wzwqoo/fmcw_10ghz_radar/rf_frontend/ads/3RX_coupling.png

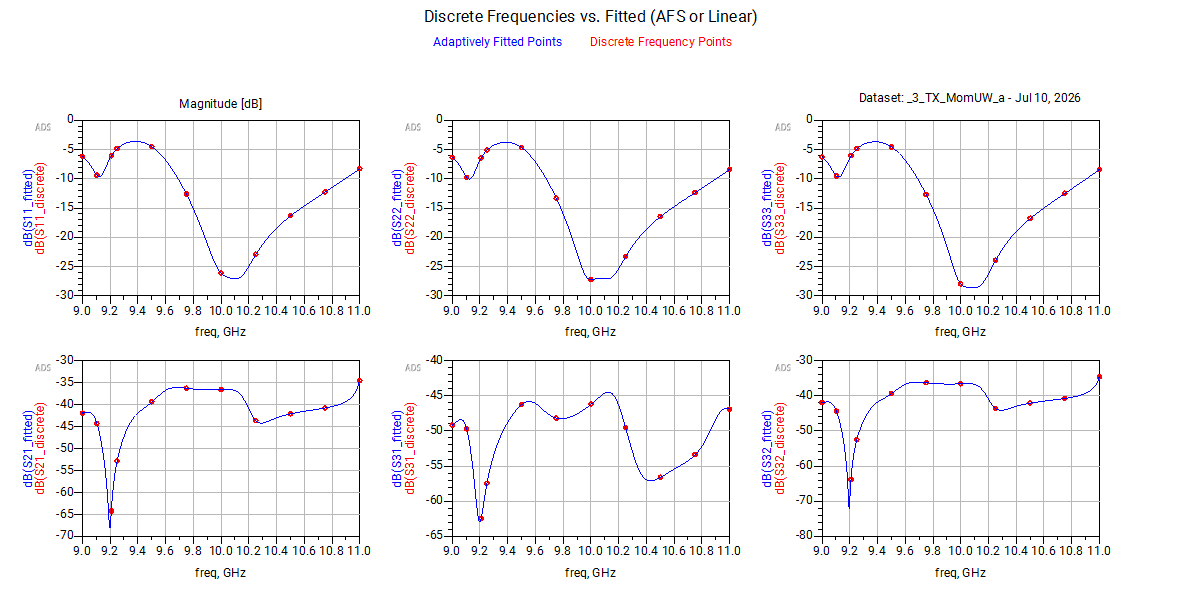
rf_frontend/ads/3RX_coupling.png
