wzwqoo/fmcw_10ghz_radar/rf_frontend/ads/LNA_gain.png

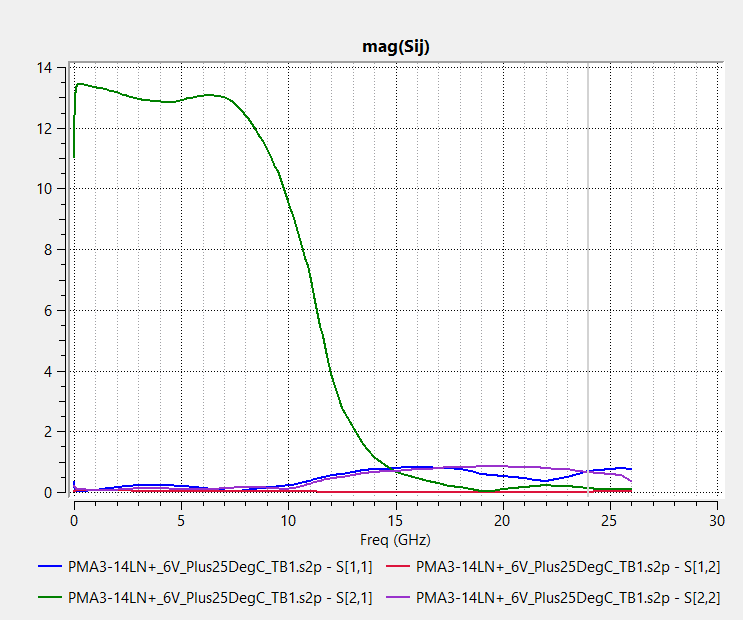
rf_frontend/ads/LNA_gain.png
