wzwqoo/fmcw_10ghz_radar/rf_frontend/ads/LO_tree.png

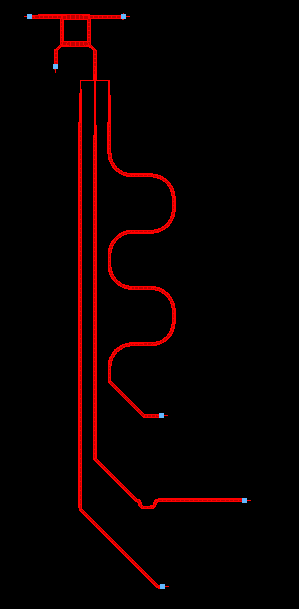
rf_frontend/ads/LO_tree.png
