wzwqoo/fmcw_10ghz_radar/rf_frontend/ads/TX_RX_isolation.png

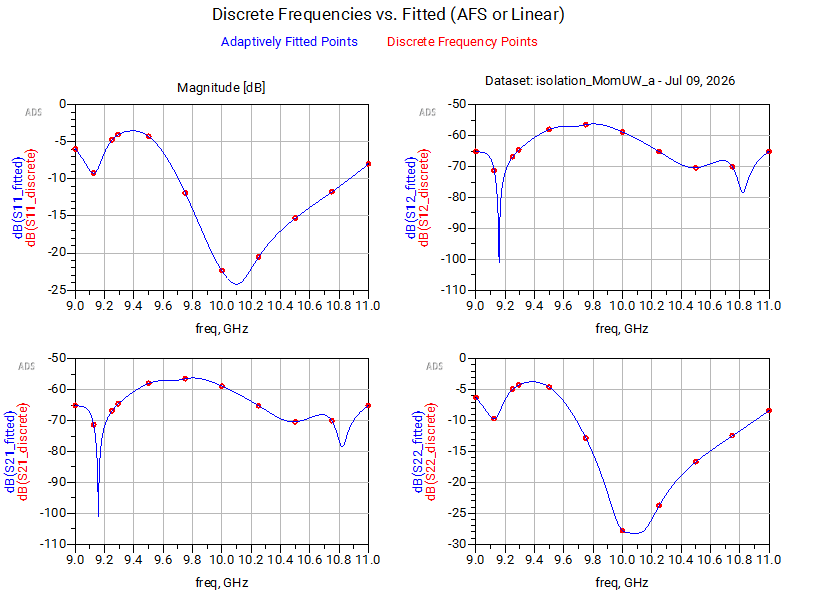
rf_frontend/ads/TX_RX_isolation.png
