wzwqoo/fmcw_10ghz_radar/rf_frontend/ads/coupler_result.png

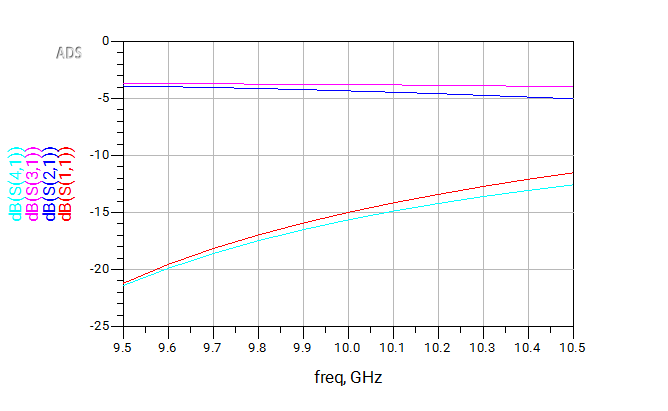
rf_frontend/ads/coupler_result.png
