wzwqoo/fmcw_10ghz_radar/rf_frontend/ads/LO_tree_result.png

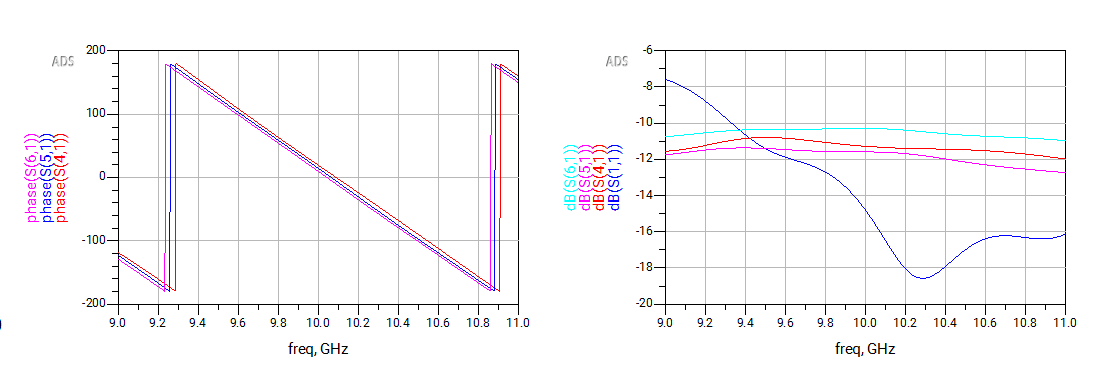
rf_frontend/ads/LO_tree_result.png
