wzwqoo/fmcw_10ghz_radar/rf_frontend/ads/patch_antenna_result.png

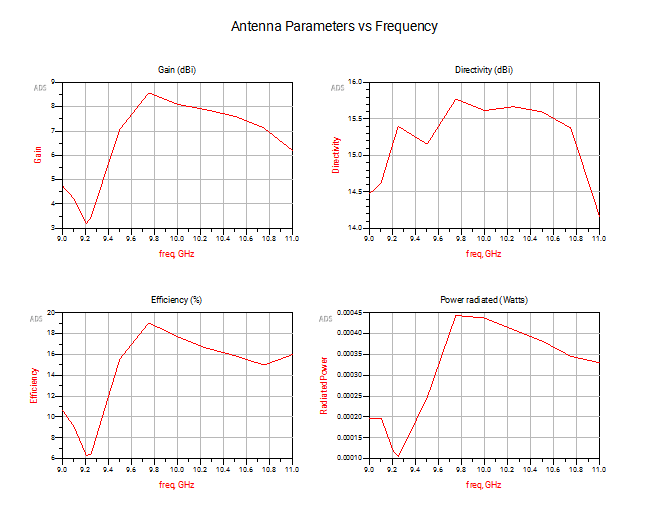
rf_frontend/ads/patch_antenna_result.png
