wzwqoo/fmcw_10ghz_radar/rf_frontend/ads/splitter_result.png

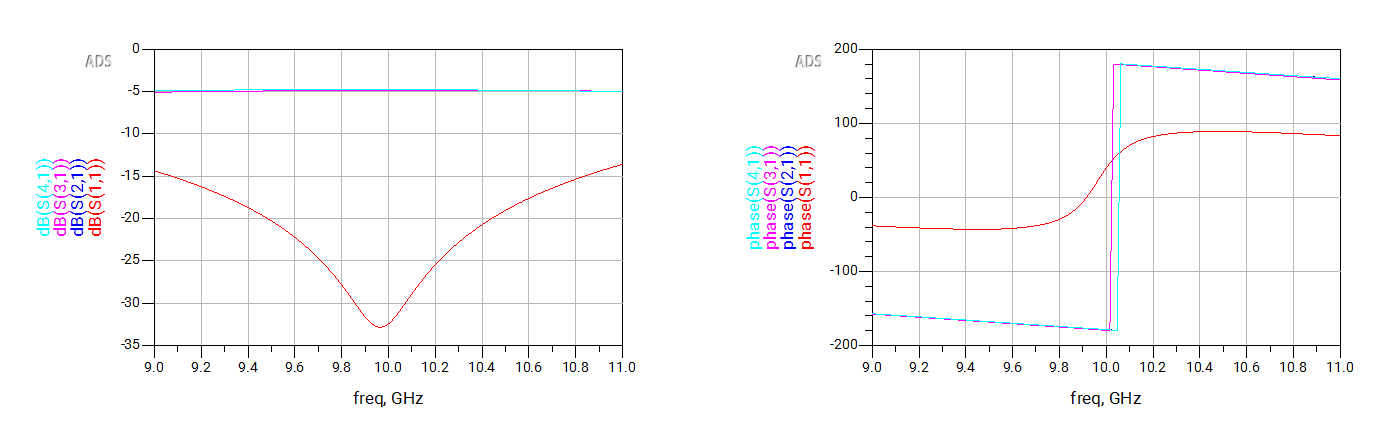
rf_frontend/ads/splitter_result.png
