wzwqoo/fmcw_10ghz_radar/carrier_board/ov9281/ETH.kicad_sch

## KiCad design carrier_board/ov9281/ETH.kicad_sch (2026-09-03)

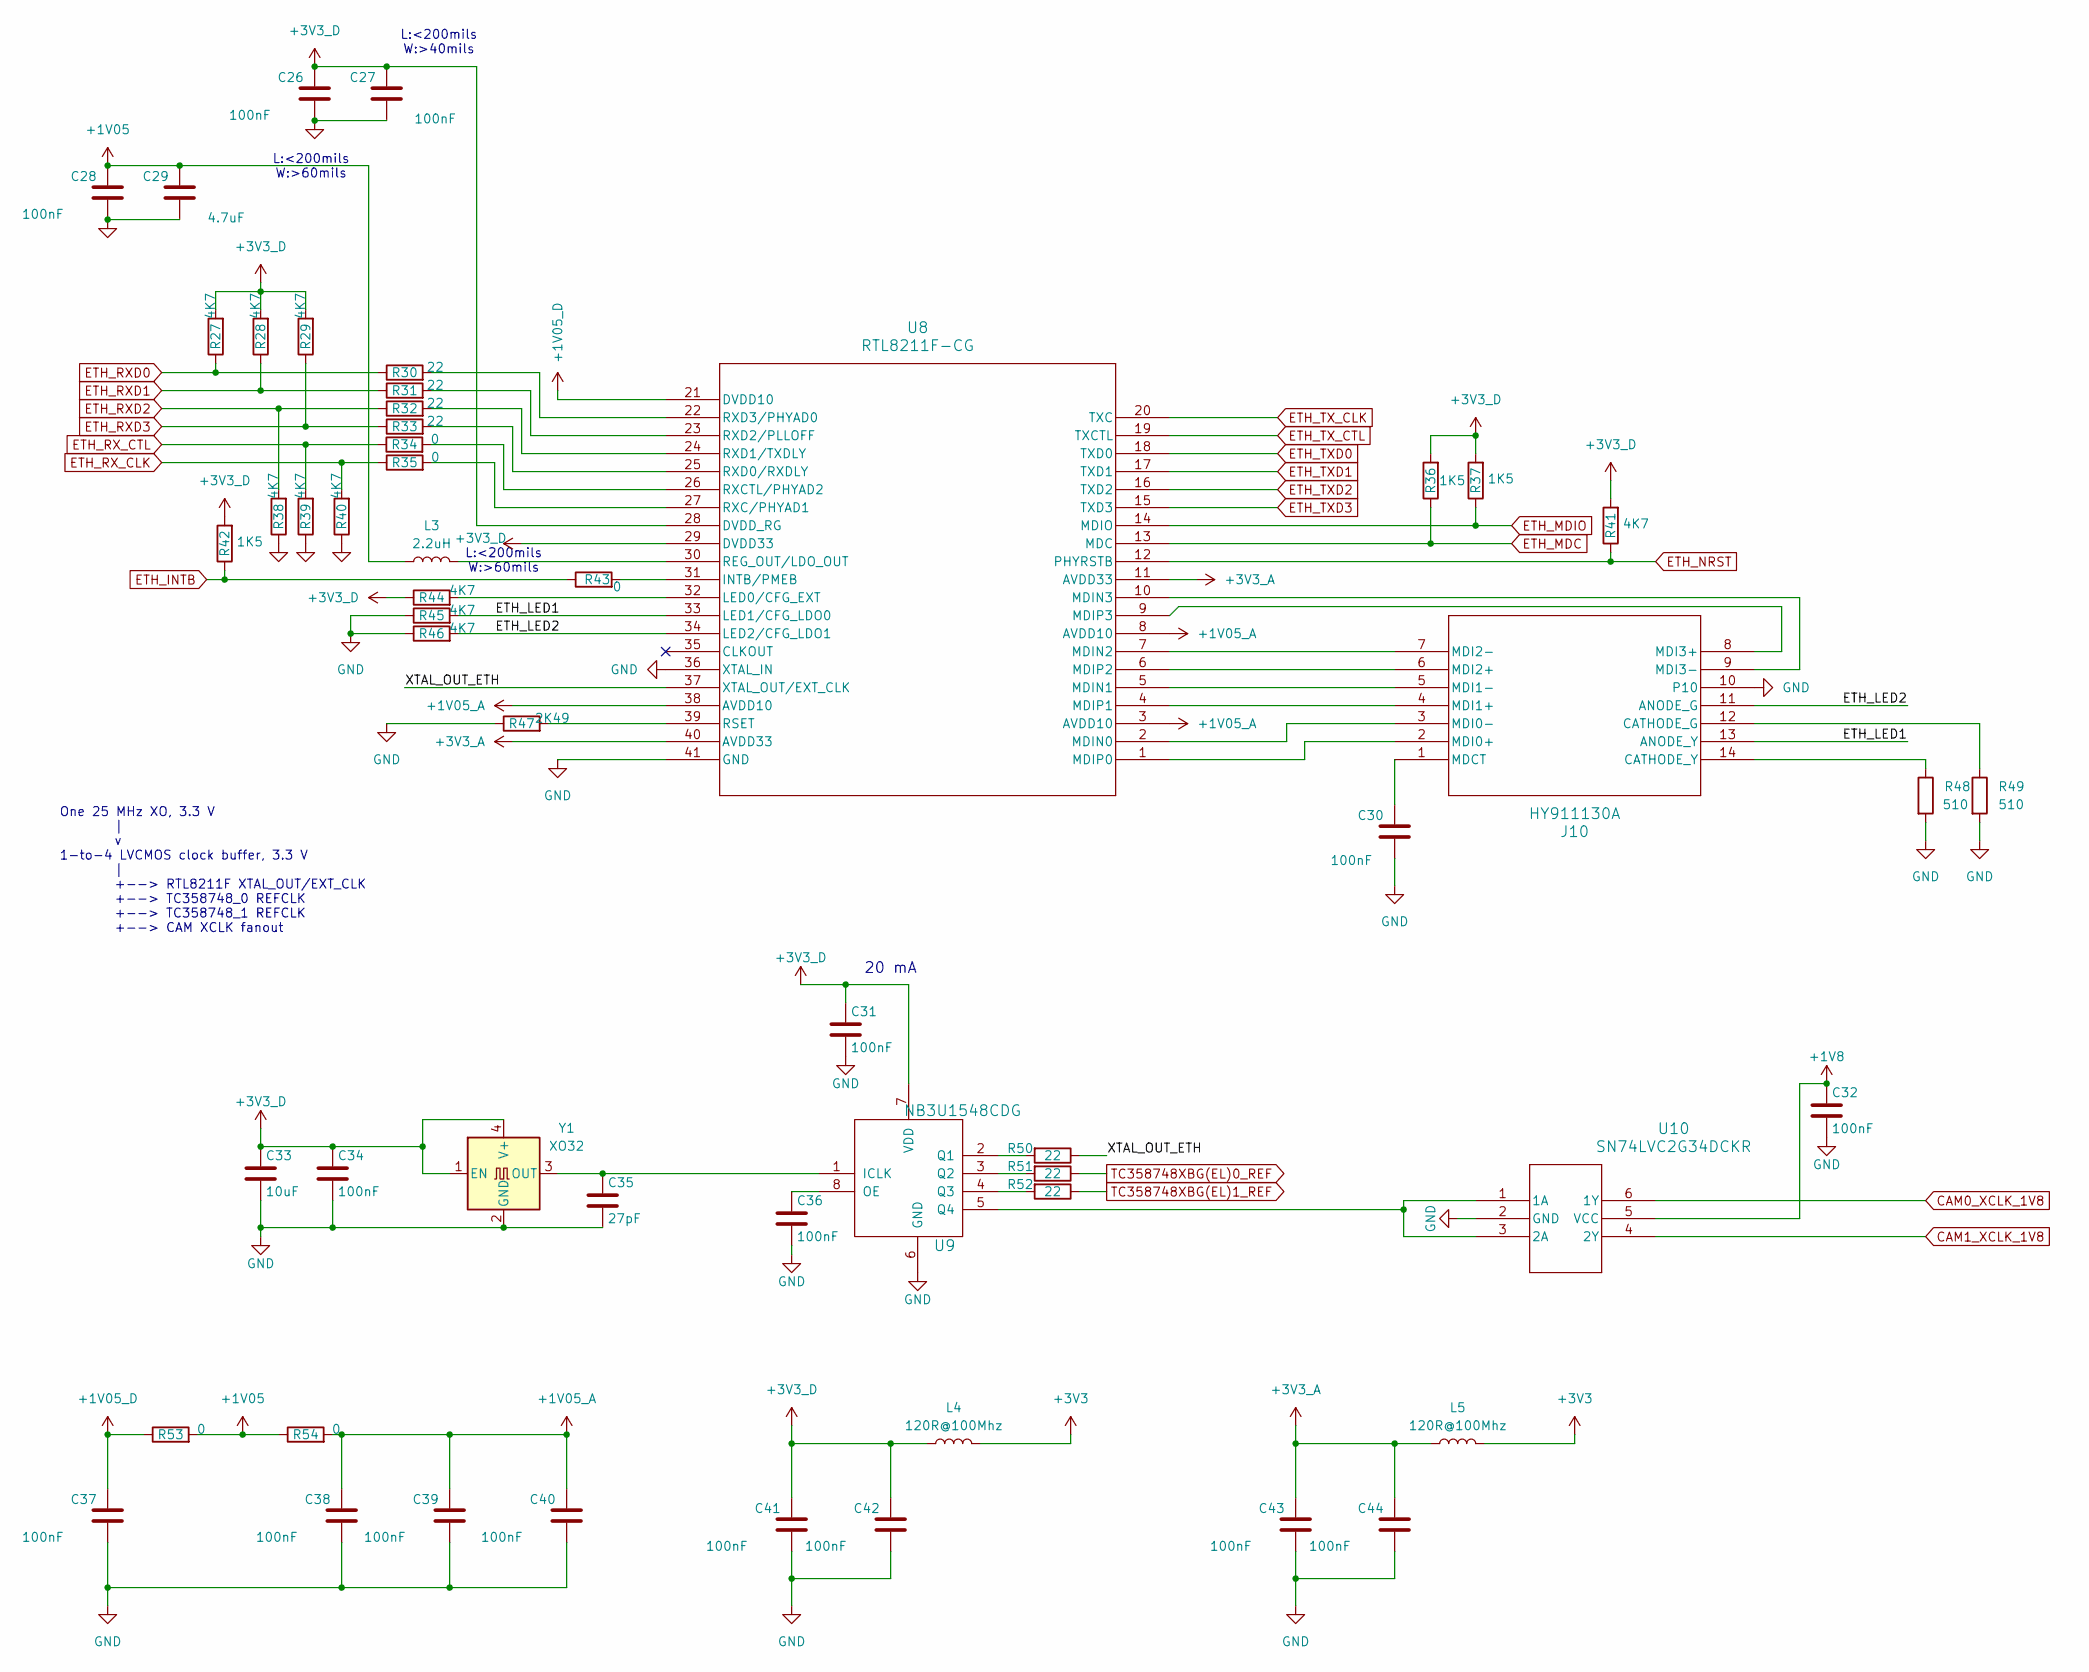
[picture p39: schematic ETH.kicad_sch]

Parts:
C26, C27, C28, C30, C31, C32, C34, C36, C37, C38, C39, C40, C41, C42, C43, C44: 100nF; C_0805_2012Metric; Part# x; LCSC Part # x
C29: 4.7uF; C_0805_2012Metric; Part# CC0805KKX7R8BB475; LCSC Part # C354262
C33: 10uF; C_0805_2012Metric; Part# CC0805KKX5R8BB106; LCSC Part # C89831
C35: 27pF; C_0805_2012Metric; Part# x; LCSC Part # x
J10: HY911130A; HY911130A_HAN; LCSC Part # C55679
L3: 2.2uH; L_0805_2012Metric; Part# MLP2012H2R2MT0S1; LCSC Part # C383369
L4, L5: 120R@100Mhz; L_0805_2012Metric; Part# UPZ2012E121-4R0TF; LCSC Part # C97001
R27, R28, R29, R38, R39, R40, R41, R44, R45, R46: 4K7; R_0805_2012Metric; Part# x; LCSC Part # x
R30, R31, R32, R33, R50, R51, R52: 22; R_0805_2012Metric; Part# RC0805JR-0722RL; LCSC Part # C108406
R34, R35, R43, R53, R54: 0; R_0805_2012Metric; Part# RC0805JR-070RL; LCSC Part # C96345
R36, R37, R42: 1K5; R_0805_2012Metric; Part# RC0805FR-071K5L; LCSC Part # C114555
R47: 2K49; R_0805_2012Metric; Part# AC0805FR-7W2K49L; LCSC Part # C727992
R48, R49: 510; R_0805_2012Metric; Part# RC0805FR-07510RL; LCSC Part # C114563
U8: RTL8211F-CG; RTL8211F-CG_RTK; LCSC Part # C187932
U9: NB3U1548CDG; SOIC-8_5.3x5.3mm_P1.27mm; LCSC Part # C603365
U10: SN74LVC2G34DCKR; SOT-363_SC-70-6; LCSC Part # C14461
Y1: XO32; Oscillator_SMD_EuroQuartz_XO32-4Pin_3.2x2.5mm; Part# OT322525MJBA4SL; LCSC Part # C669088

Connections:
+1V05: C28.1, C29.1, L3.1, R53.2, R54.1
+1V05_A: C38.1, C39.1, C40.1, R54.2, U8.3 (AVDD10), U8.8 (AVDD10), U8.38 (AVDD10)
+1V05_D: C37.1, R53.1, U8.21 (DVDD10)
+1V8: C32.1, U10.5 (VCC)
+3V3: L4.2, L5.2
+3V3_A: C43.1, C44.1, L5.1, U8.11 (AVDD33), U8.40 (AVDD33)
+3V3_D: C26.1, C27.1, C31.1, C33.1, C34.1, C41.1, C42.1, L4.1, R27.2, R28.2, R29.2, R36.2, R37.2, R41.2, R42.2, R44.1, U8.28 (DVDD_RG), U8.29 (DVDD33), U9.7 (VDD), Y1.1 (EN), Y1.4 (V+)
CAM0_XCLK_1V8: U10.6 (1Y)
CAM1_XCLK_1V8: U10.4 (2Y)
ETH_INTB: R42.1, R43.1
ETH_LED1: J10.13 (ANODE_Y), R45.2, U8.33 (LED1/CFG_LDO0)
ETH_LED2: J10.11 (ANODE_G), R46.2, U8.34 (LED2/CFG_LDO1)
ETH_MDC: R36.1, U8.13 (MDC)
ETH_MDIO: R37.1, U8.14 (MDIO)
ETH_NRST: R41.1, U8.12 (PHYRSTB)
ETH_RXD0: R27.1, R30.1
ETH_RXD1: R28.1, R31.1
ETH_RXD2: R32.1, R38.2
ETH_RXD3: R29.1, R33.1
ETH_RX_CLK: R35.1, R40.2
ETH_RX_CTL: R34.1, R39.2
ETH_TXD0: U8.18 (TXD0)
ETH_TXD1: U8.17 (TXD1)
ETH_TXD2: U8.16 (TXD2)
ETH_TXD3: U8.15 (TXD3)
ETH_TX_CLK: U8.20 (TXC)
ETH_TX_CTL: U8.19 (TXCTL)
GND: C26.2, C27.2, C28.2, C29.2, C30.2, C31.2, C32.2, C33.2, C34.2, C35.2, C36.2, C37.2, C38.2, C39.2, C40.2, C41.2, C42.2, C43.2, C44.2, J10.10, R38.1, R39.1, R40.1, R45.1, R46.1, R47.1, R48.2, R49.2, U8.36 (XTAL_IN), U8.41 (GND), U9.6 (GND), U10.2 (GND), Y1.2 (GND)
unnamed: C30.1, J10.1 (MDCT)
unnamed: C35.1, U9.1 (ICLK), Y1.3 (OUT)
unnamed: C36.1, U9.8 (OE)
unnamed: J10.2 (MDI0+), U8.1 (MDIP0)
unnamed: J10.3 (MDI0-), U8.2 (MDIN0)
unnamed: J10.4 (MDI1+), U8.4 (MDIP1)
unnamed: J10.5 (MDI1-), U8.5 (MDIN1)
unnamed: J10.6 (MDI2+), U8.6 (MDIP2)
unnamed: J10.7 (MDI2-), U8.7 (MDIN2)
unnamed: J10.8 (MDI3+), U8.9 (MDIP3)
unnamed: J10.9 (MDI3-), U8.10 (MDIN3)
unnamed: J10.12 (CATHODE_G), R49.1
unnamed: J10.14 (CATHODE_Y), R48.1
unnamed: L3.2, U8.30 (REG_OUT/LDO_OUT)
unnamed: R30.2, U8.22 (RXD3/PHYAD0)
unnamed: R31.2, U8.23 (RXD2/PLLOFF)
unnamed: R32.2, U8.24 (RXD1/TXDLY)
unnamed: R33.2, U8.25 (RXD0/RXDLY)
unnamed: R34.2, U8.26 (RXCTL/PHYAD2)
unnamed: R35.2, U8.27 (RXC/PHYAD1)
unnamed: R43.2, U8.31 (INTB/PMEB)
unnamed: R44.2, U8.32 (LED0/CFG_EXT)
unnamed: R47.2, U8.39 (RSET)
unnamed: R50.2, U9.2 (Q1)
unnamed: R51.2, U9.3 (Q2)
unnamed: R52.2, U9.4 (Q3)
unnamed: U9.5 (Q4), U10.1 (1A), U10.3 (2A)
TC358748XBG(EL)0_REF: R51.1
TC358748XBG(EL)1_REF: R52.1
XTAL_OUT_ETH: R50.1, U8.37 (XTAL_OUT/EXT_CLK)

Notes on the sheet:
L:<200mils W:>40mils
L:<200mils W:>60mils
One 25 MHz XO, 3.3 V | v 1-to-4 LVCMOS clock buffer, 3.3 V | +--> RTL8211F XTAL_OUT/EXT_CLK +--> TC358748_0 REFCLK +--> TC358748_1 REFCLK +--> CAM XCLK fanout
20 mA
