wzwqoo/fmcw_10ghz_radar/carrier_board/ov9281/FMCW.kicad_sch

## KiCad design carrier_board/ov9281/FMCW.kicad_sch (2026-09-03)

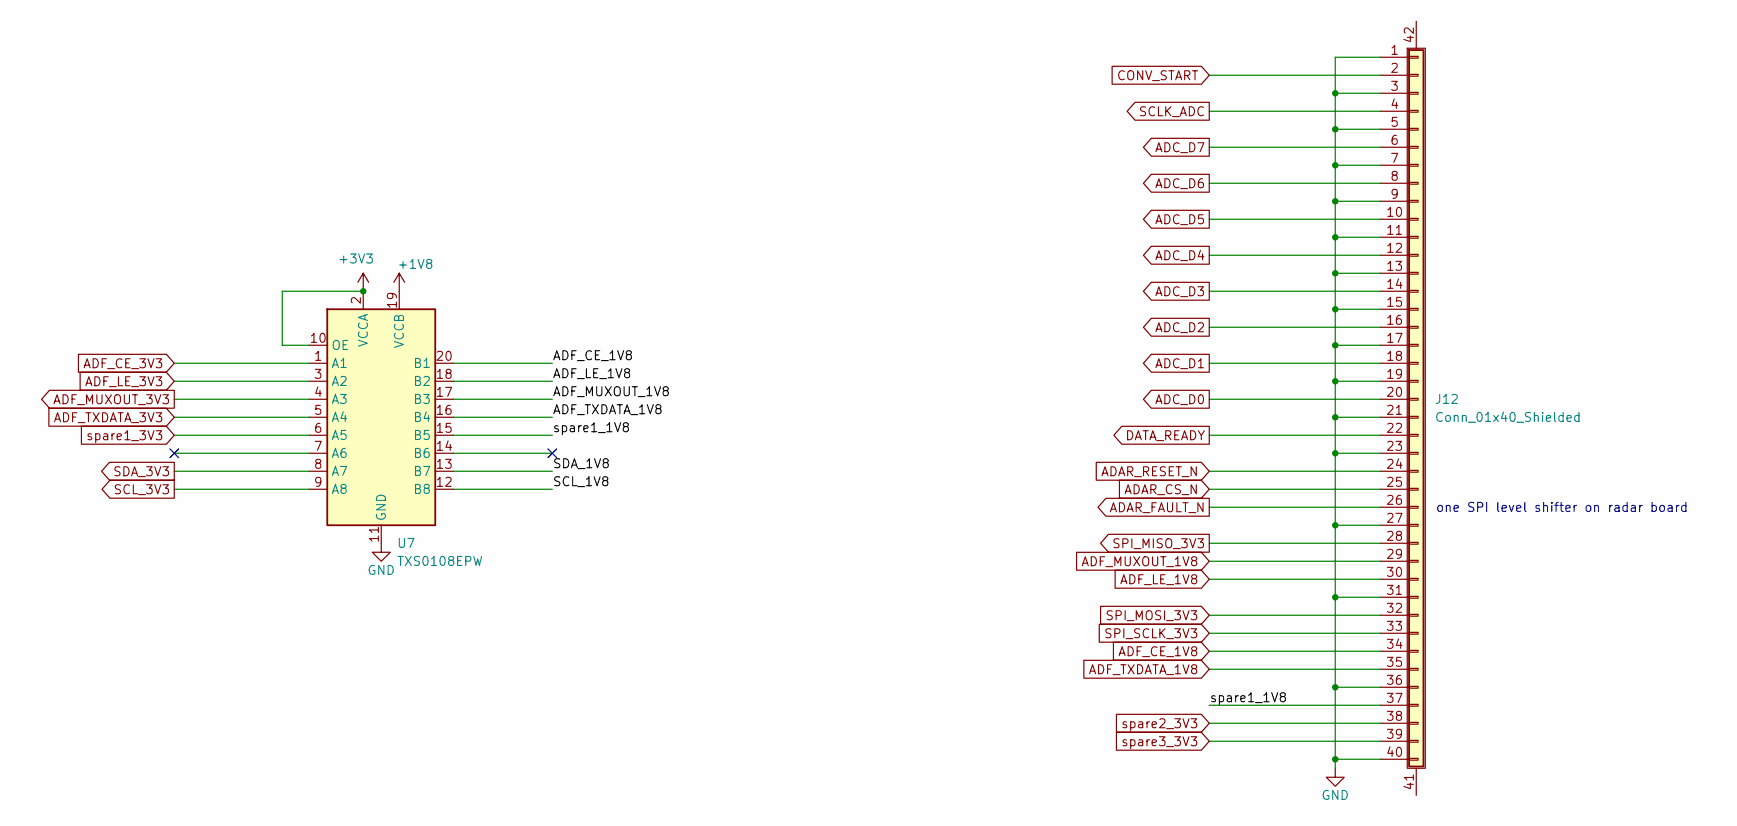
[picture p40: schematic FMCW.kicad_sch]

Parts:
J12: Conn_01x40_Shielded; FPC-SMD_40P-P0.50_XUNPU_FPC-05FB-40PH20; Part# FPC-05FB-40PH20; LCSC Part # C2856837
U7: TXS0108EPW; TSSOP-20_4.4x6.5mm_P0.65mm; LCSC Part # C17206

Connections:
+1V8: U7.19 (VCCB)
+3V3: U7.2 (VCCA), U7.10 (OE)
ADAR_CS_N: J12.25
ADAR_FAULT_N: J12.26
ADAR_RESET_N: J12.24
ADC_D0: J12.20
ADC_D1: J12.18
ADC_D2: J12.16
ADC_D3: J12.14
ADC_D4: J12.12
ADC_D5: J12.10
ADC_D6: J12.8
ADC_D7: J12.6
ADF_CE_1V8: J12.34, U7.20 (B1)
ADF_CE_3V3: U7.1 (A1)
ADF_LE_1V8: J12.30, U7.18 (B2)
ADF_LE_3V3: U7.3 (A2)
ADF_MUXOUT_1V8: J12.29, U7.17 (B3)
ADF_MUXOUT_3V3: U7.4 (A3)
ADF_TXDATA_1V8: J12.35, U7.16 (B4)
ADF_TXDATA_3V3: U7.5 (A4)
CONV_START: J12.2
DATA_READY: J12.22
GND: J12.1, J12.3, J12.5, J12.7, J12.9, J12.11, J12.13, J12.15, J12.17, J12.19, J12.21, J12.23, J12.27, J12.31, J12.36, J12.40, U7.11 (GND)
SCLK_ADC: J12.4
SCL_1V8: U7.12 (B8)
SCL_3V3: U7.9 (A8)
SDA_1V8: U7.13 (B7)
SDA_3V3: U7.8 (A7)
SPI_MISO_3V3: J12.28
SPI_MOSI_3V3: J12.32
SPI_SCLK_3V3: J12.33
spare1_1V8: J12.37, U7.15 (B5)
spare1_3V3: U7.6 (A5)
spare2_3V3: J12.38
spare3_3V3: J12.39

Notes on the sheet:
one SPI level shifter on radar board
