wzwqoo/fmcw_10ghz_radar/carrier_board/ov9281/FPGA.kicad_sch

## KiCad design carrier_board/ov9281/FPGA.kicad_sch (2026-09-03)

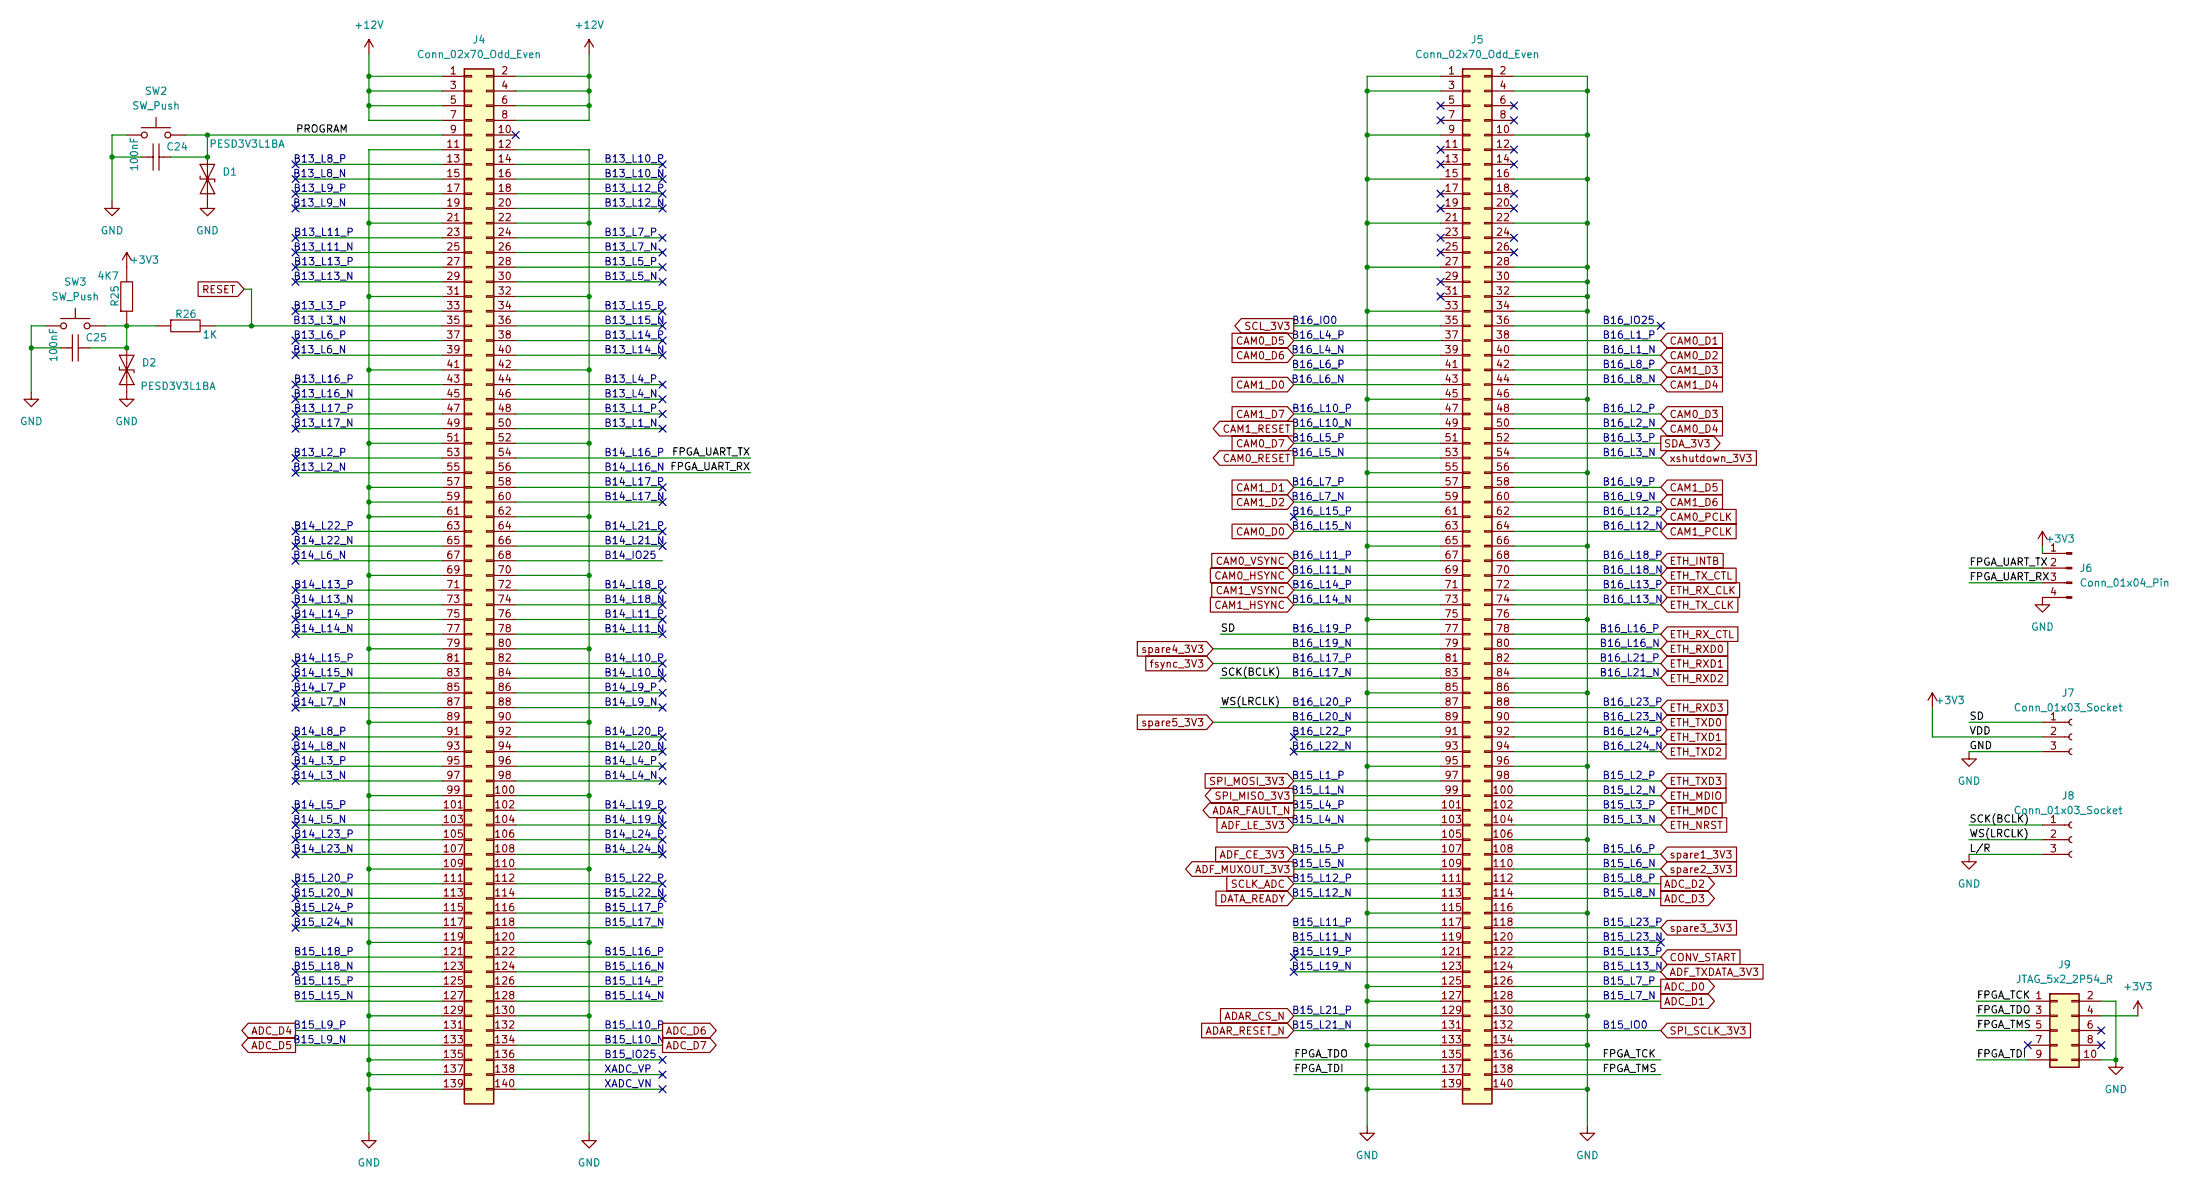
[picture p41: schematic FPGA.kicad_sch]

Parts:
C24, C25: 100nF; C_0805_2012Metric; TOLERANCE ±10%; RATINGS 16V; X7R; MANUFACTURER PART NUMBE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 CC0402KRX7R7BB103; LCSC Part # x
D1, D2: PESD3V3L1BA; D_SOD-323; Part# PESD3V3L1BA; LCSC Part # C54334012
J4, J5: Conn_02x70_Odd_Even; CONN-SMD_140P-P0.50_B2BM-2X70-0P5_BZOOC; Part# x; LCSC Part # x
J6: Conn_01x04_Pin; PinHeader_1x04_P2.54mm_Vertical; Part# x; LCSC Part # x
J7, J8: Conn_01x03_Socket; PinSocket_1x03_P2.54mm_Vertical; Part# x; LCSC Part # x
J9: JTAG_5x2_2P54_R; PinHeader_2x05_P2.54mm_Horizontal; Part# TSW-105-08-F-D-RA; LCSC Part # C6292590
R25: 4K7; R_0805_2012Metric; RATINGS 1/16 W; TOLERANCE ±5%; MANUFACTURER PART NUMBE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 RC0402JR-073K3L; LCSC Part # x
R26: 1K; R_0805_2012Metric; RATINGS 1/16 W; TOLERANCE ±5%; MANUFACTURER PART NUMBE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 RC0402JR-073K3L; LCSC Part # C100046
SW2, SW3: SW_Push; SW_Push_SPST_NO_Alps_SKRK; Part# SKRKAHE020; LCSC Part # C202388

Connections:
+3V3: J6.1, J7.2, J9.4, R25.2
+12V: J4.1, J4.2, J4.3, J4.4, J4.5, J4.6, J4.7, J4.8
ADAR_CS_N: J5.129
ADAR_FAULT_N: J5.101
ADAR_RESET_N: J5.131
ADC_D0: J5.126
ADC_D1: J5.128
ADC_D2: J5.112
ADC_D3: J5.114
ADC_D4: J4.131
ADC_D5: J4.133
ADC_D6: J4.132
ADC_D7: J4.134
ADF_CE_3V3: J5.107
ADF_LE_3V3: J5.103
ADF_MUXOUT_3V3: J5.109
ADF_TXDATA_3V3: J5.124
CAM0_D0: J5.63
CAM0_D1: J5.38
CAM0_D2: J5.40
CAM0_D3: J5.48
CAM0_D4: J5.50
CAM0_D5: J5.37
CAM0_D6: J5.39
CAM0_D7: J5.51
CAM0_HSYNC: J5.69
CAM0_PCLK: J5.62
CAM0_RESET: J5.53
CAM0_VSYNC: J5.67
CAM1_D0: J5.43
CAM1_D1: J5.57
CAM1_D2: J5.59
CAM1_D3: J5.42
CAM1_D4: J5.44
CAM1_D5: J5.58
CAM1_D6: J5.60
CAM1_D7: J5.47
CAM1_HSYNC: J5.73
CAM1_PCLK: J5.64
CAM1_RESET: J5.49
CAM1_VSYNC: J5.71
CONV_START: J5.122
DATA_READY: J5.113
ETH_INTB: J5.68
ETH_MDC: J5.102
ETH_MDIO: J5.100
ETH_NRST: J5.104
ETH_RXD0: J5.80
ETH_RXD1: J5.82
ETH_RXD2: J5.84
ETH_RXD3: J5.88
ETH_RX_CLK: J5.72
ETH_RX_CTL: J5.78
ETH_TXD0: J5.90
ETH_TXD1: J5.92
ETH_TXD2: J5.94
ETH_TXD3: J5.98
ETH_TX_CLK: J5.74
ETH_TX_CTL: J5.70
FPGA_TCK: J5.136, J9.1
FPGA_TDI: J5.137, J9.9
FPGA_TDO: J5.135, J9.3
FPGA_TMS: J5.138, J9.5
FPGA_UART_RX: J4.56, J6.3
FPGA_UART_TX: J4.54, J6.2
GND: C24.2, C25.2, D1.1 (A1), D2.1 (A1), J4.11, J4.12, J4.21, J4.22, J4.31, J4.32, J4.41, J4.42, J4.51, J4.52, J4.57, J4.59, J4.61, J4.62, J4.69, J4.70, J4.79, J4.80, J4.89, J4.90, J4.99, J4.100, J4.109, J4.110, J4.119, J4.120, J4.129, J4.130, J4.135, J4.137, J4.139, J5.1, J5.2, J5.3, J5.4, J5.9, J5.10, J5.15, J5.16, J5.21, J5.22, J5.27, J5.28, J5.30, J5.32, J5.33, J5.34, J5.45, J5.46, J5.55, J5.56, J5.65, J5.66, J5.75, J5.76, J5.85, J5.86, J5.95, J5.96, J5.105, J5.106, J5.115, J5.116, J5.125, J5.127, J5.130, J5.133, J5.134, J5.139, J5.140, J6.4, J7.3, J8.3, J9.2, J9.10, SW2.1, SW3.1
unnamed: C25.1, D2.2 (A2), R25.1, R26.1, SW3.2
PROGRAM: C24.1, D1.2 (A2), J4.9, SW2.2
RESET: J4.35, R26.2
SCK(BCLK): J5.83, J8.1
SCLK_ADC: J5.111
SCL_3V3: J5.35
SD: J5.77, J7.1
SDA_3V3: J5.52
SPI_MISO_3V3: J5.99
SPI_MOSI_3V3: J5.97
SPI_SCLK_3V3: J5.132
WS(LRCLK): J5.87, J8.2
fsync_3V3: J5.81
spare1_3V3: J5.108
spare2_3V3: J5.110
spare3_3V3: J5.118
spare4_3V3: J5.79
spare5_3V3: J5.89
xshutdown_3V3: J5.54

Notes on the sheet:
B16_L14_N
B14_L24_P
B14_L15_P
B16_L1_P
B14_L22_N
B15_L5_P
B16_L3_P
B16_L13_N
B15_L17_N
B13_L6_P
B16_L21_N
B14_L14_P
B15_L1_N
B13_L2_P
B15_L24_P
B15_L15_P
B14_IO25
B16_L20_P
B14_L18_P
B13_L13_N
B16_L24_N
B15_L7_P
B13_L16_N
B13_L13_P
B15_L11_N
B15_L21_N
B15_L22_P
B15_L20_P
B13_L1_P
B14_L9_P
B13_L4_P
B13_L14_N
B15_L14_P
B15_L24_N
B16_L11_P
B14_L3_P
B15_L8_N
B13_L8_N
B13_L14_P
B15_L23_P
B16_L24_P
B14_L22_P
B13_L11_P
B16_L3_N
B16_L18_N
B16_L19_N
B16_L21_P
B15_IO25
B15_L1_P
B16_L7_P
B13_L17_N
B16_L10_P
B16_L9_P
B16_L15_N
B13_L11_N
B16_L22_N
B16_L12_N
B15_L12_P
B16_L9_N
B16_L2_N
B15_L16_N
B15_L13_N
B14_L13_N
B14_L17_P
B14_L10_N
B14_L4_P
B15_L19_P
B15_L8_P
B15_L2_P
B13_L15_P
B16_L17_N
B16_L19_P
B15_L10_N
B16_L17_P
B15_L9_P
B13_L3_N
B16_L2_P
B14_L6_N
B14_L7_P
B16_L22_P
B13_L3_P
B13_L12_P
B16_L1_N
B16_L4_N
B15_L12_N
B14_L5_P
B15_L6_N
B14_L11_N
B15_L4_P
B14_L4_N
B13_L5_P
B14_L3_N
B15_L15_N
B15_L18_N
XADC_VN
B14_L10_P
B16_L5_N
B16_L4_P
B14_L24_N
B14_L20_N
B16_L13_P
B13_L8_P
B13_L15_N
B13_L9_P
B13_L2_N
B15_L16_P
B15_L3_P
B15_IO0
B15_L10_P
B14_L21_P
B16_L5_P
B16_L16_P
B13_L16_P
B16_L8_P
B13_L1_N
B15_L11_P
B14_L16_N
B15_L9_N
B14_L17_N
B15_L19_N
B15_L6_P
B14_L7_N
B16_L14_P
B13_L4_N
B16_IO0
B15_L18_P
B14_L23_P
B13_L7_P
B15_L17_P
B13_L12_N
B14_L5_N
B15_L22_N
B14_L23_N
B14_L13_P
B15_L4_N
B16_L6_P
B13_L7_N
B13_L6_N
B14_L20_P
B16_L23_P
B16_L6_N
B13_L17_P
B15_L20_N
B16_L7_N
B14_L8_N
B13_L5_N
B16_L20_N
B15_L2_N
XADC_VP
B15_L23_N
B14_L16_P
B14_L9_N
B14_L11_P
B15_L3_N
B16_L15_P
B14_L19_P
B16_L23_N
B15_L21_P
B16_IO25
B16_L18_P
B14_L8_P
B15_L5_N
B15_L14_N
B13_L9_N
B16_L8_N
B13_L10_P
B14_L21_N
B14_L15_N
B16_L16_N
B16_L12_P
B13_L10_N
B16_L11_N
B16_L10_N
B14_L14_N
B15_L13_P
B15_L7_N
B14_L18_N
B14_L19_N
