wzwqoo/fmcw_10ghz_radar/carrier_board/ov9281/extension.kicad_sch

## KiCad design carrier_board/ov9281/extension.kicad_sch (2026-09-03)

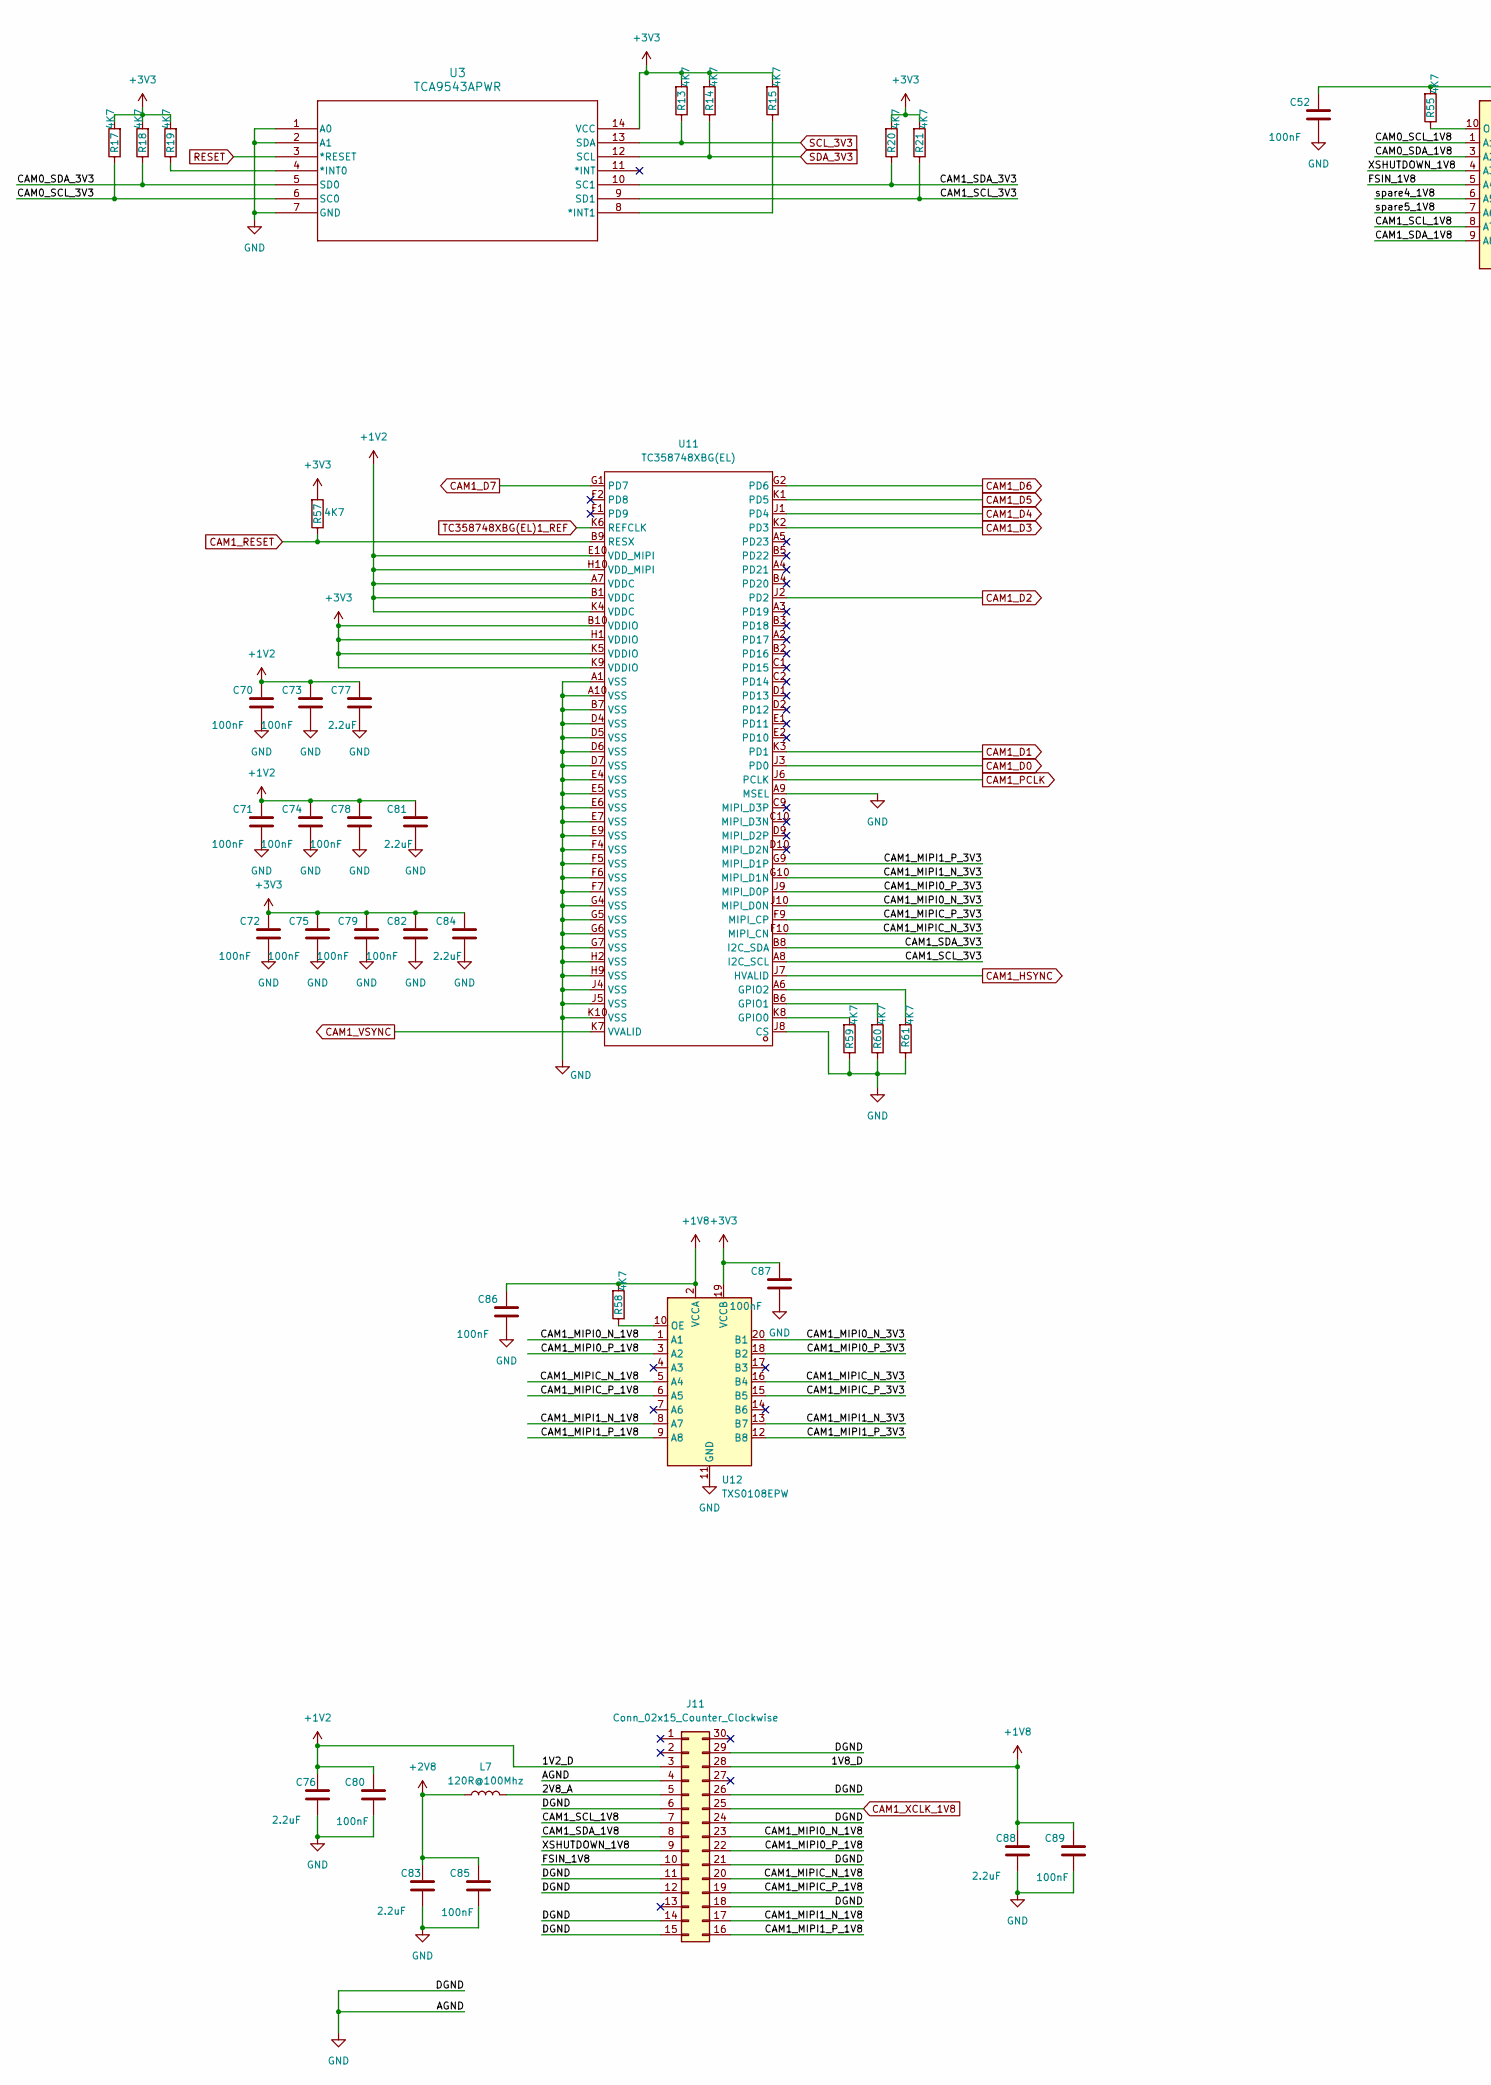
[picture p42: schematic extension.kicad_sch, part in row 1, column 1]

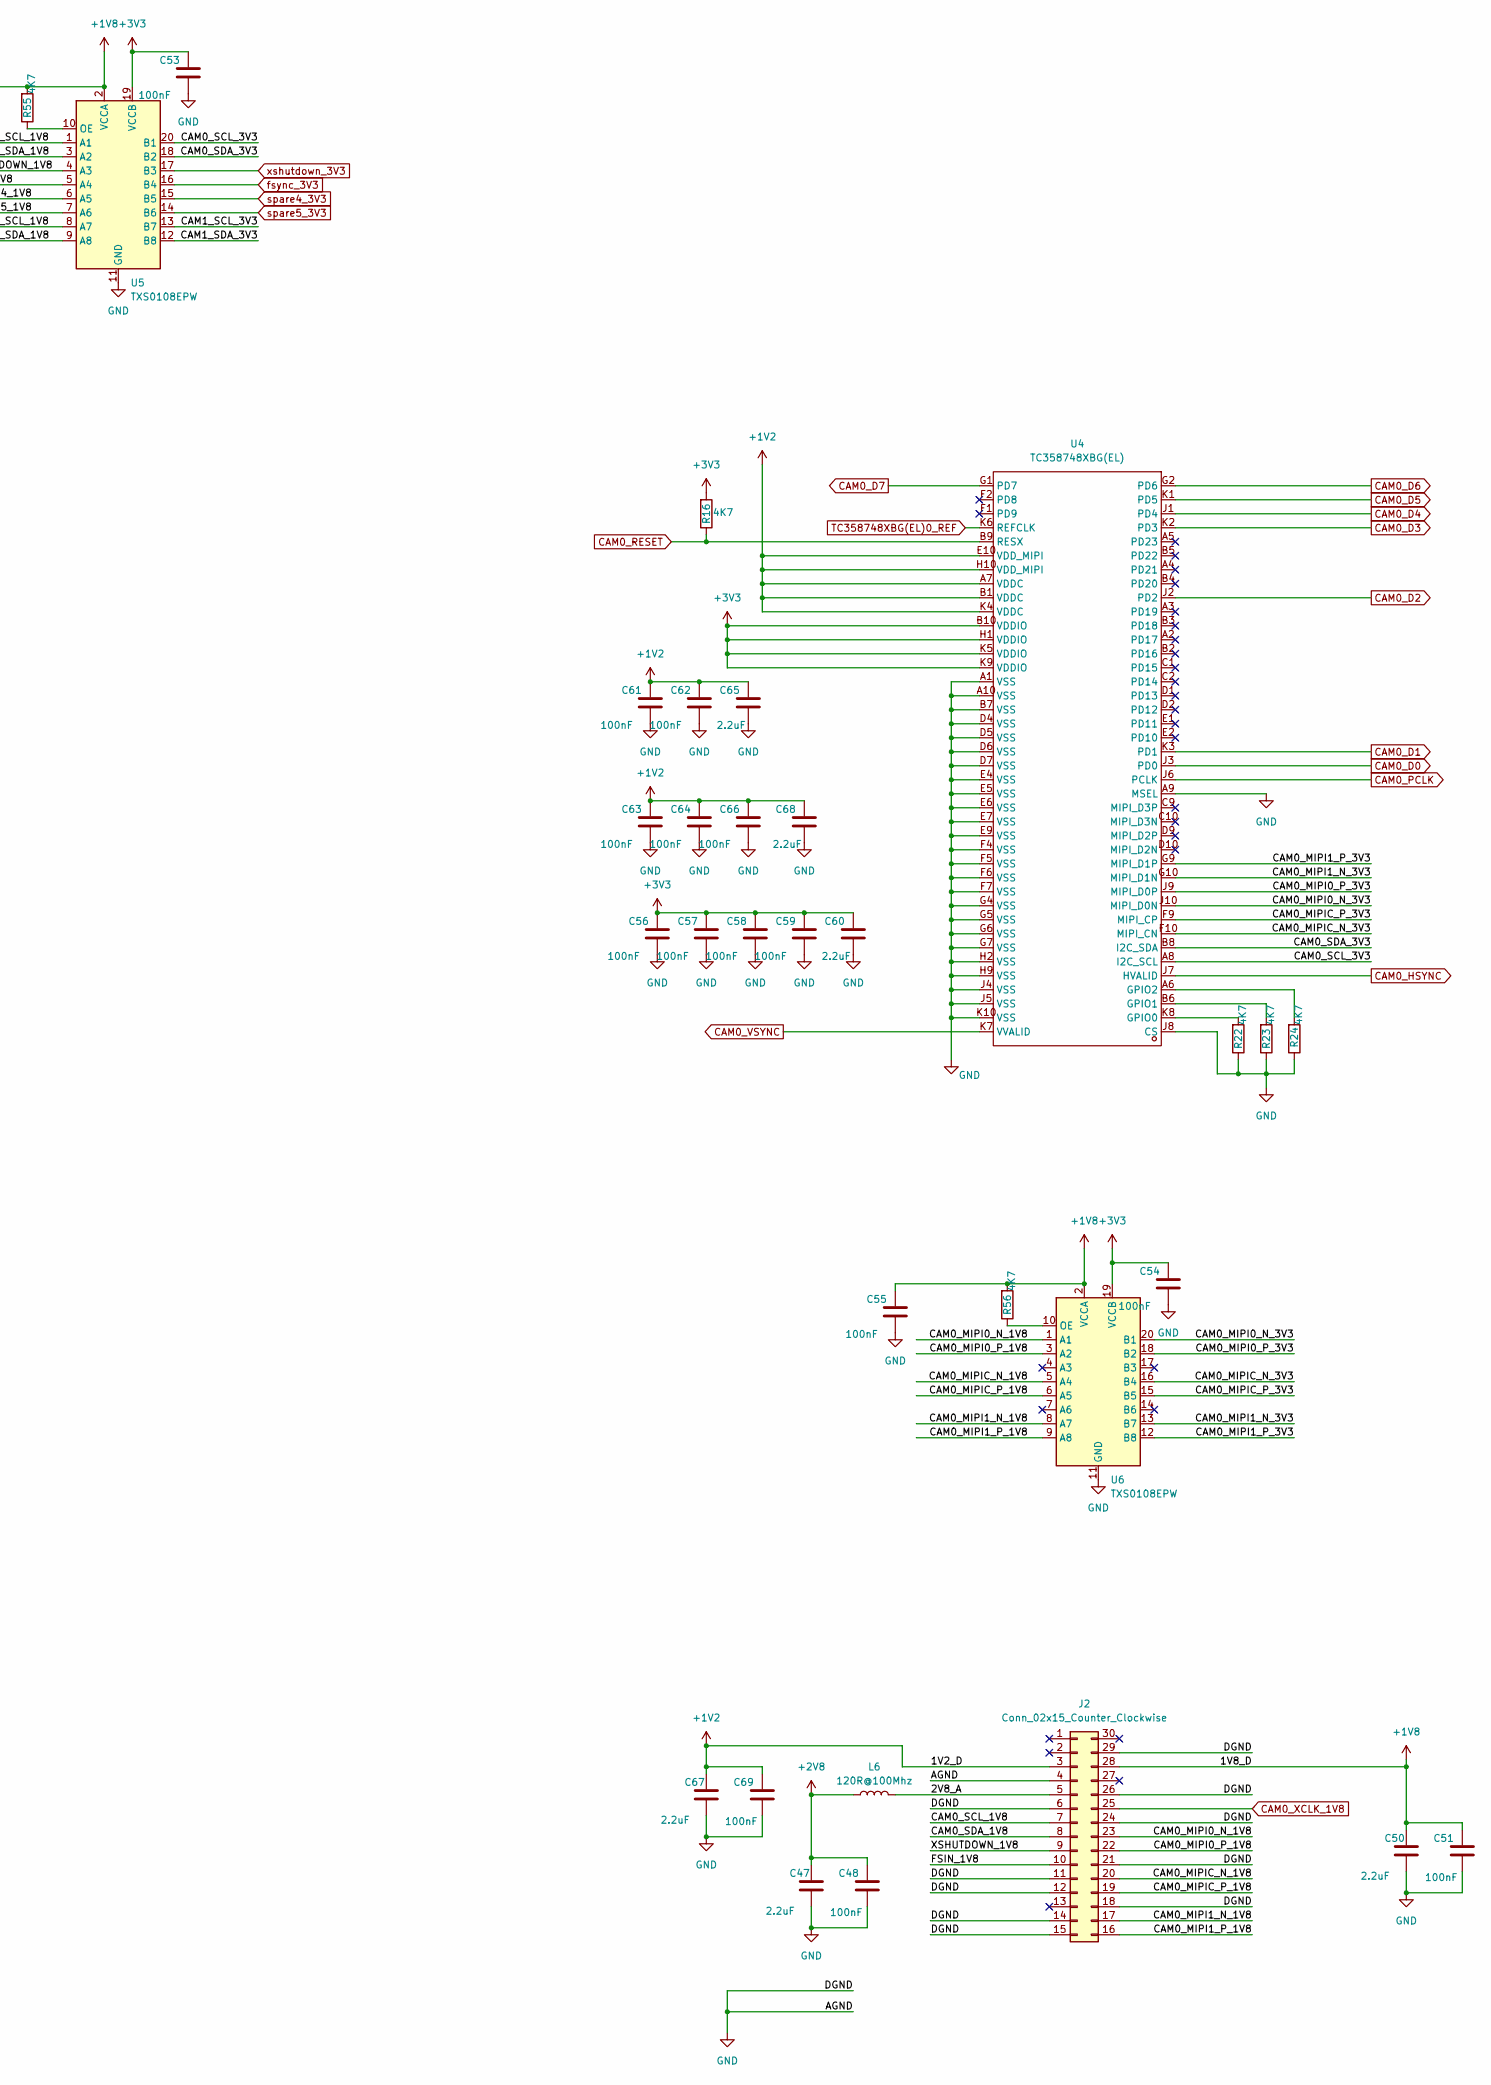
[picture p43: schematic extension.kicad_sch, part in row 1, column 2]

Parts:
C47, C50, C60, C65, C67, C68, C76, C77, C81, C83, C84, C88: 2.2uF; C_0805_2012Metric; Part# x; LCSC Part # x
C48, C51, C52, C53, C54, C55, C56, C57, C58, C59, C61, C62, C63, C64, C66, C69, C70, C71, C72, C73, C74, C75, C78, C79, C80, C82, C85, C86, C87, C89: 100nF; C_0805_2012Metric; Part# x; LCSC Part # x
J2, J11: Conn_02x15_Counter_Clockwise; Part# x; LCSC Part # x
L6, L7: 120R@100Mhz; L_0805_2012Metric; Part# UPZ2012E121-4R0TF; LCSC Part # C97001
R13, R14, R15, R16, R17, R18, R19, R20, R21, R22, R23, R24, R55, R56, R57, R58, R59, R60, R61: 4K7; R_0805_2012Metric; Part# x; LCSC Part # x
U3: TCA9543APWR; TSSOP-14_4.4x5mm_P0.65mm; LCSC Part # C2653307
U4, U11: TC358748XBG(EL); P-VFBGA-80_L7.0-W7.0-R10-C10-P0.65-TL; LCSC Part # C5447096
U5, U6, U12: TXS0108EPW; TSSOP-20_4.4x6.5mm_P0.65mm; LCSC Part # C17206

Connections:
2V8_A: J2.5, J11.5, L6.2, L7.2
+1V2: C61.1, C62.1, C63.1, C64.1, C65.1, C66.1, C67.1, C68.1, C69.1, C70.1, C71.1, C73.1, C74.1, C76.1, C77.1, C78.1, C80.1, C81.1, J2.3, J11.3, U4.A7 (VDDC), U4.B1 (VDDC), U4.E10 (VDD_MIPI), U4.H10 (VDD_MIPI), U4.K4 (VDDC), U11.A7 (VDDC), U11.B1 (VDDC), U11.E10 (VDD_MIPI), U11.H10 (VDD_MIPI), U11.K4 (VDDC)
+1V8: C50.1, C51.1, C52.1, C55.1, C86.1, C88.1, C89.1, J2.28, J11.28, R55.2, R56.2, R58.2, U5.2 (VCCA), U6.2 (VCCA), U12.2 (VCCA)
+2V8: C47.1, C48.1, C83.1, C85.1, L6.1, L7.1
+3V3: C53.1, C54.1, C56.1, C57.1, C58.1, C59.1, C60.1, C72.1, C75.1, C79.1, C82.1, C84.1, C87.1, R13.2, R14.2, R15.2, R16.2, R17.2, R18.2, R19.2, R20.2, R21.2, R57.2, U3.14 (VCC), U4.B10 (VDDIO), U4.H1 (VDDIO), U4.K5 (VDDIO), U4.K9 (VDDIO), U5.19 (VCCB), U6.19 (VCCB), U11.B10 (VDDIO), U11.H1 (VDDIO), U11.K5 (VDDIO), U11.K9 (VDDIO), U12.19 (VCCB)
CAM0_D0: U4.J3 (PD0)
CAM0_D1: U4.K3 (PD1)
CAM0_D2: U4.J2 (PD2)
CAM0_D3: U4.K2 (PD3)
CAM0_D4: U4.J1 (PD4)
CAM0_D5: U4.K1 (PD5)
CAM0_D6: U4.G2 (PD6)
CAM0_D7: U4.G1 (PD7)
CAM0_HSYNC: U4.J7 (HVALID)
CAM0_MIPI0_N_1V8: J2.23, U6.1 (A1)
CAM0_MIPI0_N_3V3: U4.J10 (MIPI_D0N), U6.20 (B1)
CAM0_MIPI0_P_1V8: J2.22, U6.3 (A2)
CAM0_MIPI0_P_3V3: U4.J9 (MIPI_D0P), U6.18 (B2)
CAM0_MIPI1_N_1V8: J2.17, U6.8 (A7)
CAM0_MIPI1_N_3V3: U4.G10 (MIPI_D1N), U6.13 (B7)
CAM0_MIPI1_P_1V8: J2.16, U6.9 (A8)
CAM0_MIPI1_P_3V3: U4.G9 (MIPI_D1P), U6.12 (B8)
CAM0_MIPIC_N_1V8: J2.20, U6.5 (A4)
CAM0_MIPIC_N_3V3: U4.F10 (MIPI_CN), U6.16 (B4)
CAM0_MIPIC_P_1V8: J2.19, U6.6 (A5)
CAM0_MIPIC_P_3V3: U4.F9 (MIPI_CP), U6.15 (B5)
CAM0_PCLK: U4.J6 (PCLK)
CAM0_RESET: R16.1, U4.B9 (RESX)
CAM0_SCL_1V8: J2.7, U5.1 (A1)
CAM0_SCL_3V3: R17.1, U3.6 (SC0), U4.A8 (I2C_SCL), U5.20 (B1)
CAM0_SDA_1V8: J2.8, U5.3 (A2)
CAM0_SDA_3V3: R18.1, U3.5 (SD0), U4.B8 (I2C_SDA), U5.18 (B2)
CAM0_VSYNC: U4.K7 (VVALID)
CAM0_XCLK_1V8: J2.25
CAM1_D0: U11.J3 (PD0)
CAM1_D1: U11.K3 (PD1)
CAM1_D2: U11.J2 (PD2)
CAM1_D3: U11.K2 (PD3)
CAM1_D4: U11.J1 (PD4)
CAM1_D5: U11.K1 (PD5)
CAM1_D6: U11.G2 (PD6)
CAM1_D7: U11.G1 (PD7)
CAM1_HSYNC: U11.J7 (HVALID)
CAM1_MIPI0_N_1V8: J11.23, U12.1 (A1)
CAM1_MIPI0_N_3V3: U11.J10 (MIPI_D0N), U12.20 (B1)
CAM1_MIPI0_P_1V8: J11.22, U12.3 (A2)
CAM1_MIPI0_P_3V3: U11.J9 (MIPI_D0P), U12.18 (B2)
CAM1_MIPI1_N_1V8: J11.17, U12.8 (A7)
CAM1_MIPI1_N_3V3: U11.G10 (MIPI_D1N), U12.13 (B7)
CAM1_MIPI1_P_1V8: J11.16, U12.9 (A8)
CAM1_MIPI1_P_3V3: U11.G9 (MIPI_D1P), U12.12 (B8)
CAM1_MIPIC_N_1V8: J11.20, U12.5 (A4)
CAM1_MIPIC_N_3V3: U11.F10 (MIPI_CN), U12.16 (B4)
CAM1_MIPIC_P_1V8: J11.19, U12.6 (A5)
CAM1_MIPIC_P_3V3: U11.F9 (MIPI_CP), U12.15 (B5)
CAM1_PCLK: U11.J6 (PCLK)
CAM1_RESET: R57.1, U11.B9 (RESX)
CAM1_SCL_1V8: J11.7, U5.8 (A7)
CAM1_SCL_3V3: R21.1, U3.9 (SD1), U5.13 (B7), U11.A8 (I2C_SCL)
CAM1_SDA_1V8: J11.8, U5.9 (A8)
CAM1_SDA_3V3: R20.1, U3.10 (SC1), U5.12 (B8), U11.B8 (I2C_SDA)
CAM1_VSYNC: U11.K7 (VVALID)
CAM1_XCLK_1V8: J11.25
FSIN_1V8: J2.10, J11.10, U5.5 (A4)
GND: C47.2, C48.2, C50.2, C51.2, C52.2, C53.2, C54.2, C55.2, C56.2, C57.2, C58.2, C59.2, C60.2, C61.2, C62.2, C63.2, C64.2, C65.2, C66.2, C67.2, C68.2, C69.2, C70.2, C71.2, C72.2, C73.2, C74.2, C75.2, C76.2, C77.2, C78.2, C79.2, C80.2, C81.2, C82.2, C83.2, C84.2, C85.2, C86.2, C87.2, C88.2, C89.2, J2.4, J2.6, J2.11, J2.12, J2.14, J2.15, J2.18, J2.21, J2.24, J2.26, J2.29, J11.4, J11.6, J11.11, J11.12, J11.14, J11.15, J11.18, J11.21, J11.24, J11.26, J11.29, R22.1, R23.1, R24.1, R59.1, R60.1, R61.1, U3.1 (A0), U3.2 (A1), U3.7 (GND), U4.A1 (VSS), U4.A9 (MSEL), U4.A10 (VSS), U4.B7 (VSS), U4.D4 (VSS), U4.D5 (VSS), U4.D6 (VSS), U4.D7 (VSS), U4.E4 (VSS), U4.E5 (VSS), U4.E6 (VSS), U4.E7 (VSS), U4.E9 (VSS), U4.F4 (VSS), U4.F5 (VSS), U4.F6 (VSS), U4.F7 (VSS), U4.G4 (VSS), U4.G5 (VSS), U4.G6 (VSS), U4.G7 (VSS), U4.H2 (VSS), U4.H9 (VSS), U4.J4 (VSS), U4.J5 (VSS), U4.J8 (CS), U4.K10 (VSS), U5.11 (GND), U6.11 (GND), U11.A1 (VSS), U11.A9 (MSEL), U11.A10 (VSS), U11.B7 (VSS), U11.D4 (VSS), U11.D5 (VSS), U11.D6 (VSS), U11.D7 (VSS), U11.E4 (VSS), U11.E5 (VSS), U11.E6 (VSS), U11.E7 (VSS), U11.E9 (VSS), U11.F4 (VSS), U11.F5 (VSS), U11.F6 (VSS), U11.F7 (VSS), U11.G4 (VSS), U11.G5 (VSS), U11.G6 (VSS), U11.G7 (VSS), U11.H2 (VSS), U11.H9 (VSS), U11.J4 (VSS), U11.J5 (VSS), U11.J8 (CS), U11.K10 (VSS), U12.11 (GND)
unnamed: R15.1, U3.8 (*INT1)
unnamed: R19.1, U3.4 (*INT0)
unnamed: R22.2, U4.K8 (GPIO0)
unnamed: R23.2, U4.B6 (GPIO1)
unnamed: R24.2, U4.A6 (GPIO2)
unnamed: R55.1, U5.10 (OE)
unnamed: R56.1, U6.10 (OE)
unnamed: R58.1, U12.10 (OE)
unnamed: R59.2, U11.K8 (GPIO0)
unnamed: R60.2, U11.B6 (GPIO1)
unnamed: R61.2, U11.A6 (GPIO2)
RESET: U3.3 (*RESET)
SCL_3V3: R13.1, U3.13 (SDA)
SDA_3V3: R14.1, U3.12 (SCL)
TC358748XBG(EL)0_REF: U4.K6 (REFCLK)
TC358748XBG(EL)1_REF: U11.K6 (REFCLK)
XSHUTDOWN_1V8: J2.9, J11.9, U5.4 (A3)
fsync_3V3: U5.16 (B4)
spare4_1V8: U5.6 (A5)
spare4_3V3: U5.15 (B5)
spare5_1V8: U5.7 (A6)
spare5_3V3: U5.14 (B6)
xshutdown_3V3: U5.17 (B3)
