wzwqoo/fmcw_10ghz_radar/carrier_board/ov9281/power.kicad_sch

## KiCad design carrier_board/ov9281/power.kicad_sch (2026-09-03)

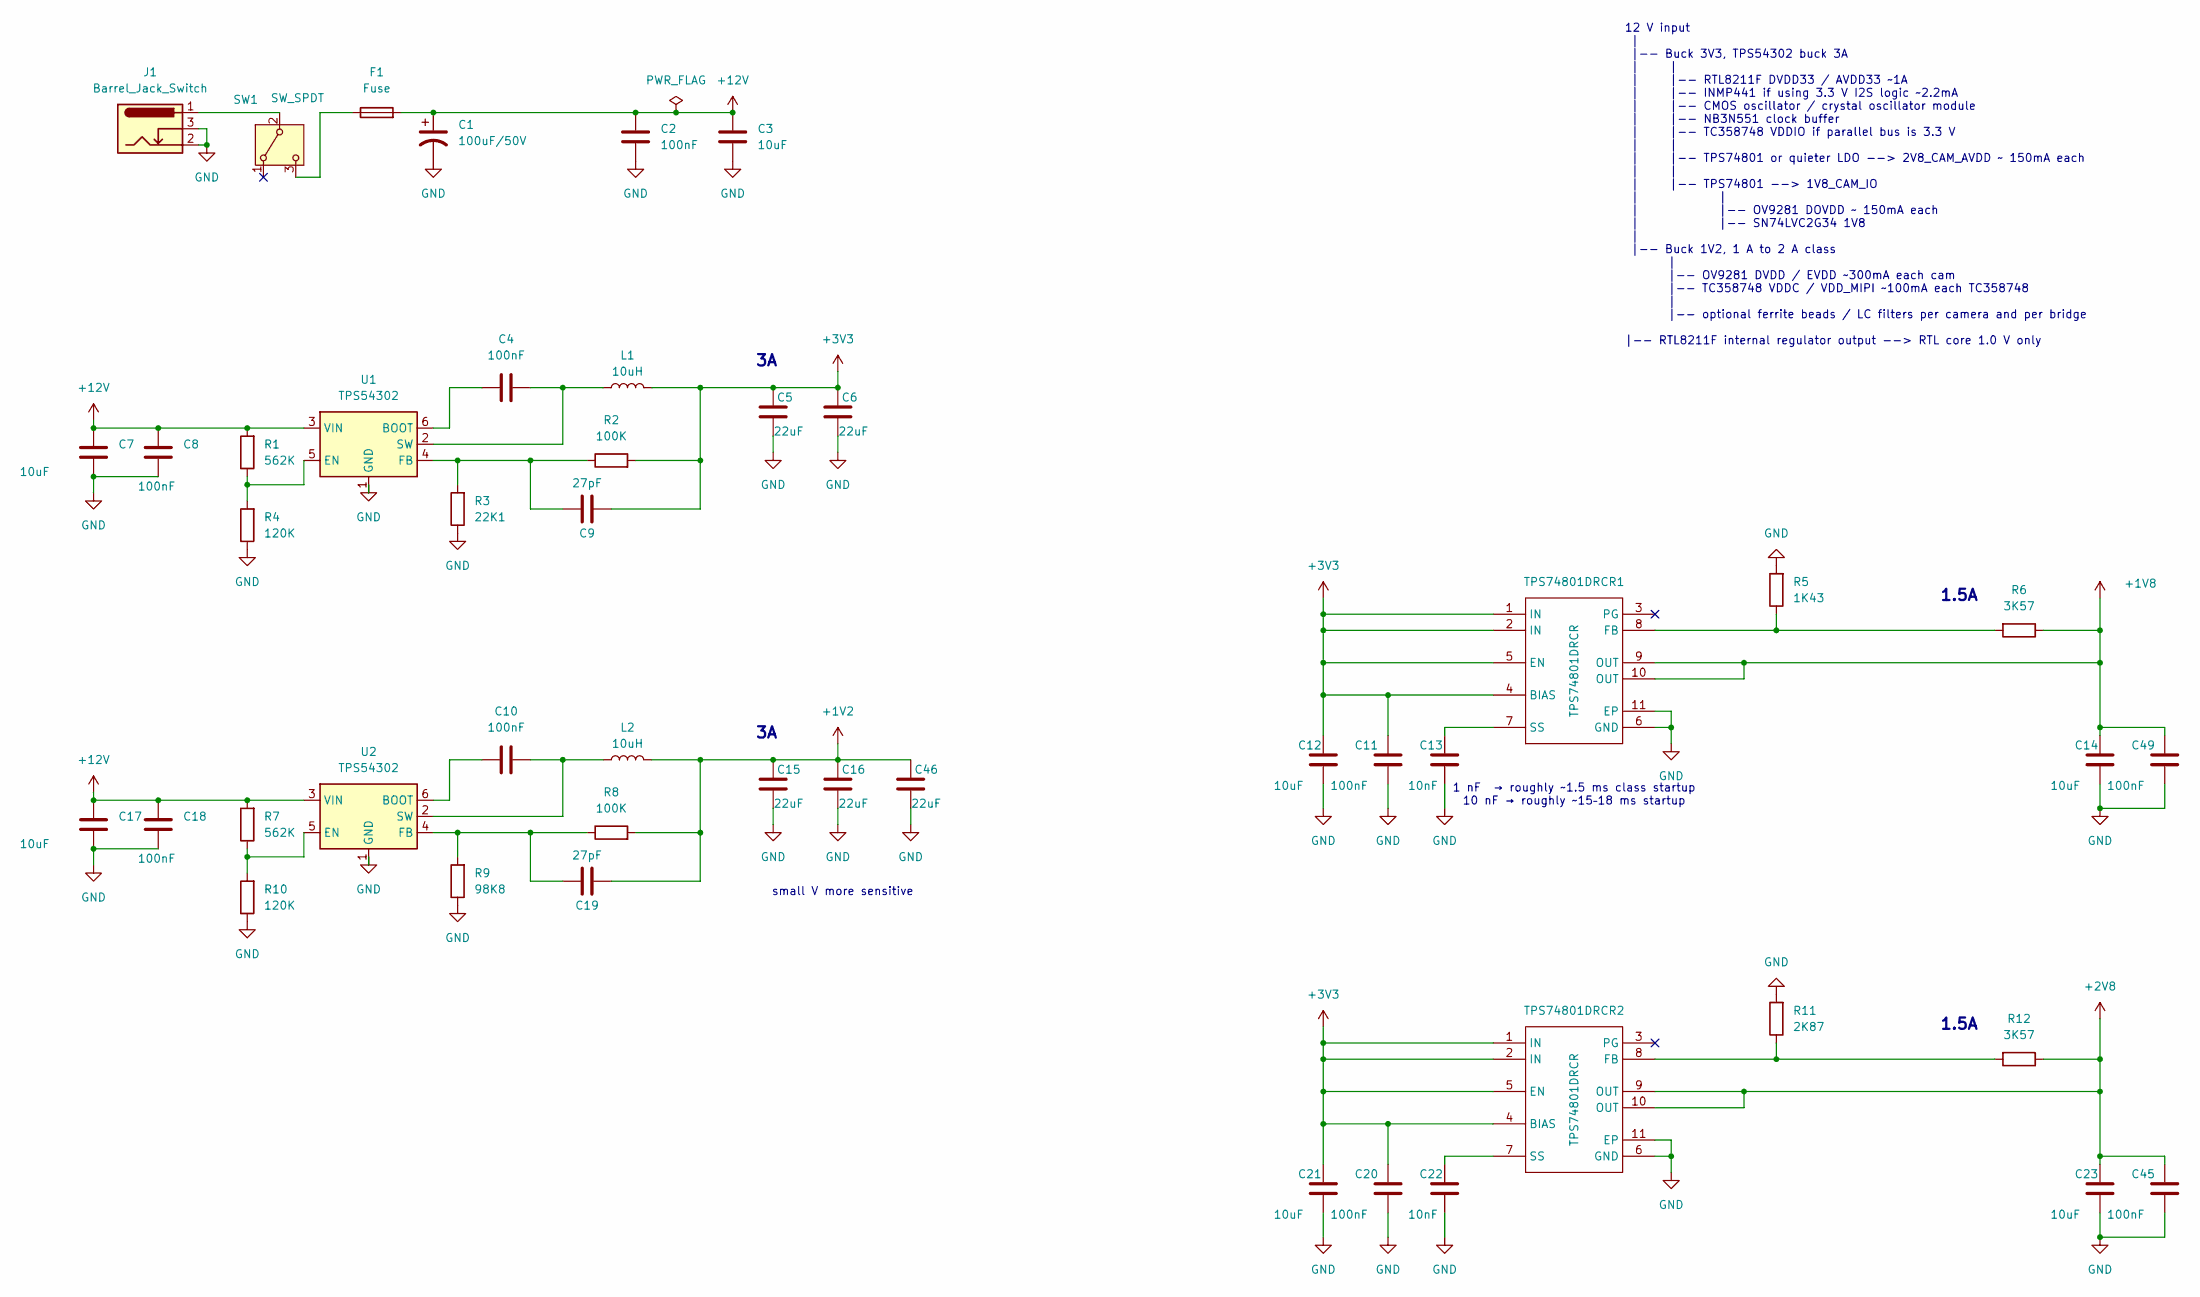
[picture p44: schematic power.kicad_sch]

Parts:
C1: 100uF/50V; CP_Elec_6.3x7.7; Part# JVJ50V100M6x8; LCSC Part # C46550415
C2, C4, C8, C10, C11, C18, C20, C45, C49: 100nF; C_0805_2012Metric; Part# x; LCSC Part # x
C3, C7, C12, C14, C17, C21, C23: 10uF; C_0805_2012Metric; Part# CC0805KKX5R8BB106; LCSC Part # C89831
C5, C6, C15, C16, C46: 22uF; C_0805_2012Metric; Part# CC0805MKX5R8BB226; LCSC Part # C784585
C9, C19: 27pF; C_0805_2012Metric; Part# x; LCSC Part # x
C13, C22: 10nF; C_0805_2012Metric; Part# x; LCSC Part # x
F1: Fuse; Fuse_1812_4532Metric; Part# SMD1812P200TF16; LCSC Part # C20812
J1: Barrel_Jack_Switch; DC-IN-TH_DC-509-ARL200-H142; Part# DC-509-ARL200-H142; LCSC Part # C34388683
L1, L2: 10uH; L_Sunlord_MWSA0602S; Part# FXL0630-100-M; LCSC Part # C167223
R1, R7: 562K; R_0805_2012Metric; Part# x; LCSC Part # x
R2, R8: 100K; R_0805_2012Metric; Part# RC0805FR-07100KL; LCSC Part # C96346
R3: 22K1; R_0805_2012Metric; Part# RC0805FR-0722K1L; LCSC Part # C273840
R4, R10: 120K; R_0805_2012Metric; Part# RC0805FR-07120KL; LCSC Part # C114524
R5: 1K43; R_0805_2012Metric; Part# RC0805FR-071K43L-S; LCSC Part # C327311
R6, R12: 3K57; R_0805_2012Metric; Part# AC0805FR-073K57L; LCSC Part # C228796
R9: 98K8; R_0402_1005Metric; Part# RT0402BRE0798K8L; LCSC Part # C853444
R11: 2K87; R_0805_2012Metric; Part# RT0805BRD072K87L; LCSC Part # C865381
SW1: SW_SPDT; SW-TH_3P-P4.80_HX-SS12D10G6-WJ; Part# SS12D10G6-WJ; LCSC Part # C7431059
TPS74801DRCR1, TPS74801DRCR2: TPS74801DRCR; VSON-10-1EP_3x3mm_P0.5mm_EP1.65x2.4mm_ThermalVias; LCSC Part # C105263
U1, U2: TPS54302; TSOT-23-6; Part# TPS54302DDCR; LCSC Part # C311983

Connections:
+1V2: C15.1, C16.1, C19.2, C46.1, L2.2, R8.2
+1V8: C14.1, C49.1, R6.1, TPS74801DRCR1.9 (OUT), TPS74801DRCR1.10 (OUT)
+2V8: C23.1, C45.1, R12.1, TPS74801DRCR2.9 (OUT), TPS74801DRCR2.10 (OUT)
+3V3: C5.1, C6.1, C9.2, C11.1, C12.1, C20.1, C21.1, L1.2, R2.2, TPS74801DRCR1.1 (IN), TPS74801DRCR1.2 (IN), TPS74801DRCR1.4 (BIAS), TPS74801DRCR1.5 (EN), TPS74801DRCR2.1 (IN), TPS74801DRCR2.2 (IN), TPS74801DRCR2.4 (BIAS), TPS74801DRCR2.5 (EN)
+12V: C1.1, C2.1, C3.1, C7.1, C8.1, C17.1, C18.1, F1.2, R1.2, R7.2, U1.3 (VIN), U2.3 (VIN)
GND: C1.2, C2.2, C3.2, C5.2, C6.2, C7.2, C8.2, C11.2, C12.2, C13.2, C14.2, C15.2, C16.2, C17.2, C18.2, C20.2, C21.2, C22.2, C23.2, C45.2, C46.2, C49.2, J1.2, J1.3, R3.1, R4.1, R5.2, R9.1, R10.1, R11.2, TPS74801DRCR1.6 (GND), TPS74801DRCR1.11 (EP), TPS74801DRCR2.6 (GND), TPS74801DRCR2.11 (EP), U1.1 (GND), U2.1 (GND)
unnamed: C4.1, U1.6 (BOOT)
unnamed: C4.2, L1.1, U1.2 (SW)
unnamed: C9.1, R2.1, R3.2, U1.4 (FB)
unnamed: C10.1, U2.6 (BOOT)
unnamed: C10.2, L2.1, U2.2 (SW)
unnamed: C13.1, TPS74801DRCR1.7 (SS)
unnamed: C19.1, R8.1, R9.2, U2.4 (FB)
unnamed: C22.1, TPS74801DRCR2.7 (SS)
unnamed: F1.1, SW1.3 (C)
unnamed: J1.1, SW1.2 (B)
unnamed: R1.1, R4.2, U1.5 (EN)
unnamed: R5.1, R6.2, TPS74801DRCR1.8 (FB)
unnamed: R7.1, R10.2, U2.5 (EN)
unnamed: R11.1, R12.2, TPS74801DRCR2.8 (FB)

Notes on the sheet:
small V more sensitive
1.5A
12 V input | |-- Buck 3V3, TPS54302 buck 3A | | | |-- RTL8211F DVDD33 / AVDD33 ~1A | |-- INMP441 if using 3.3 V I2S logic ~2.2mA | |-- CMOS oscillator / crystal oscillator module | |-- NB3N551 clock buffer | |-- TC358748 VDDIO if parallel bus is 3.3 V | | | |-- TPS74801 or quieter LDO --> 2V8_CAM_A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
1 nF → roughly ~1.5 ms class startup 10 nF → roughly ~15–18 ms startup
